panStamp/respira_fiware/docs/img/respira_fiware_pic06.jpg

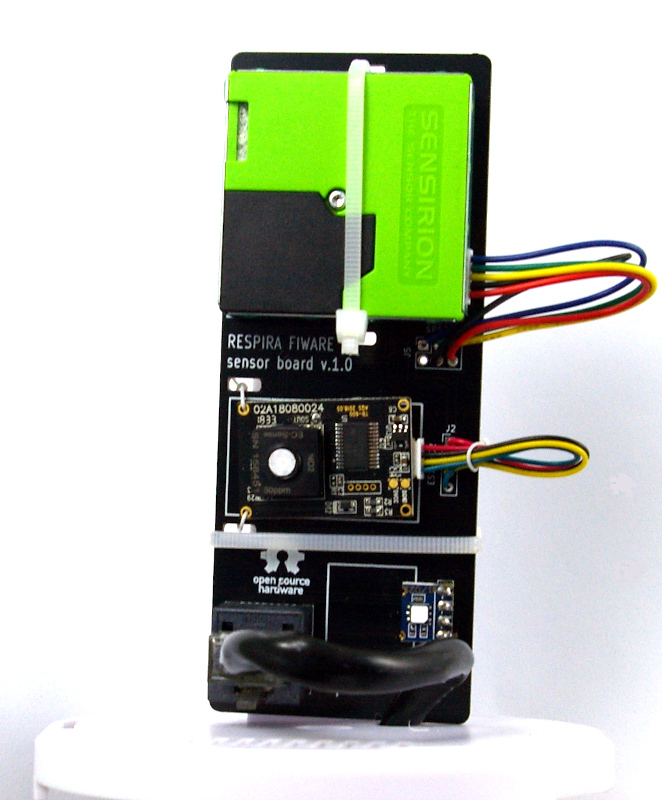
docs/img/respira_fiware_pic06.jpg
