panStamp/respira_fiware/docs/img/respira_platform_alert_panel.jpg

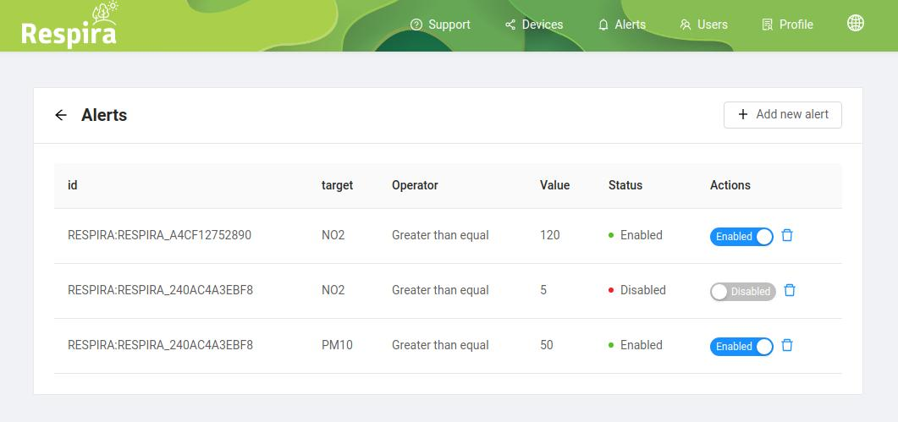
docs/img/respira_platform_alert_panel.jpg
