panStamp/respira_fiware/docs/img/respira_platform_edit_profile.jpg

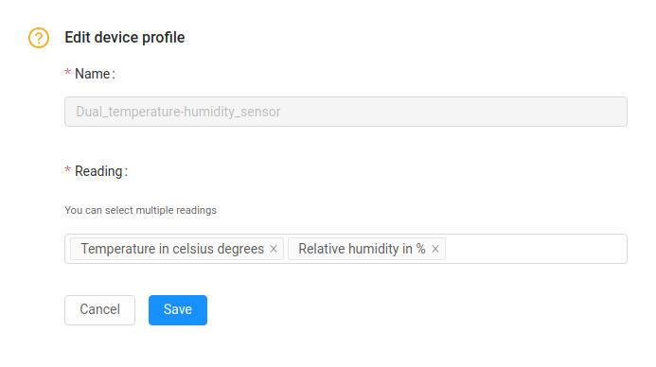
docs/img/respira_platform_edit_profile.jpg
